cfrpg/Flatcaster/doc/PadArraySim.asc

C1: cap; {Cap0}
C2: cap; {Cap0}
C3: cap; {Cap0}
C4: cap; {Cap0}
C5: cap; {Cap0}
C6: cap; {Cap0}
C7: cap; {Cap0}
C8: cap; {Cap0}
C9: cap; {Cap0}
C10: cap; {Cap1}
C11: cap; {Cap0}
C12: cap; {Cap0}
C13: cap; {Cap0}
C14: cap; {Cap0}
C15: cap; {Cap0}
C16: cap; {Cap0}
C17: cap; {Cap0}
C18: cap; {Cap0}
C19: cap; {Cap0}
C20: cap; {Cap0}
C21: cap; {Cap0}
C22: cap; {Cap0}
C23: cap; {Cap0}
C24: cap; {Cap0}
C25: cap; {Cap0}
C26: cap; {Cap0}
C27: cap; {Cap1}
C28: cap; {Cap0}
C29: cap; {Cap0}
C30: cap; {Cap0}
C31: cap; {Cap0}
C32: cap; {Cap0}
C33: cap; {Cap0}
C34: cap; {Cap0}
C35: cap; {Cap0}
C36: cap; {Cap0}
C37: cap; {Cap0}
C38: cap; {Cap0}
C39: cap; {Cap0}
C40: cap; {Cap0}
C41: cap; {Cap0}
C42: cap; {Cap0}
C43: cap; {Cap0}
C44: cap; {Cap0}
C45: cap; {Cap0}
C46: cap; {Cap0}
C47: cap; {Cap0}
C48: cap; {Cap0}
D1: schottky; BAT54
D3: schottky; BAT54
D4: schottky; BAT54
D5: schottky; BAT54
D6: schottky; BAT54
D7: schottky; BAT54
D8: schottky; BAT54
D9: schottky; BAT54
D10: schottky; BAT54
D11: schottky; BAT54
D12: schottky; BAT54
D13: schottky; BAT54
D14: schottky; BAT54
D15: schottky; BAT54
D16: schottky; BAT54
D17: schottky; BAT54
D18: schottky; BAT54
D19: schottky; BAT54
D20: schottky; BAT54
D21: schottky; BAT54
D23: schottky; BAT54
D24: schottky; BAT54
D25: schottky; BAT54
D26: schottky; BAT54
D27: schottky; BAT54
D29: schottky; BAT54
D30: schottky; BAT54
D31: schottky; BAT54
D32: schottky; BAT54
D33: schottky; BAT54
D35: schottky; BAT54
D36: schottky; BAT54
D37: schottky; BAT54
D38: schottky; BAT54
D39: schottky; BAT54
D41: schottky; BAT54
D42: schottky; BAT54
D43: schottky; BAT54
D44: schottky; BAT54
D45: schottky; BAT54
D47: schottky; BAT54
D48: schottky; BAT54
D49: schottky; BAT54
D50: schottky; BAT54
D51: schottky; BAT54
D53: schottky; BAT54
D54: schottky; BAT54
R1: res; {Res}
R2: res; {Res}
R3: res; {Res}
R4: res; {Res}
R5: res; {Res}
R6: res; {Res}
R7: res; {Res}
R8: res; {Res}
R9: res; {Res}
R10: res; {Res}
R11: res; {Res}
R12: res; {Res}
R13: res; {Res}
R14: res; {Res}
R15: res; {Res}
R16: res; {Res}
R17: res; {Res}
R18: res; {Res}
R19: res; {Res}
R20: res; {Res}
R21: res; {Res}
R22: res; {Res}
R23: res; {Res}
R24: res; {Res}
R25: res; {Res}
R26: res; {Res}
R27: res; {Res}
R28: res; {Res}
R29: res; {Res}
R30: res; {Res}
R31: res; {Res}
R32: res; {Res}
R33: res; {Res}
R34: res; {Res}
R35: res; {Res}
R36: res; {Res}
R37: res; {Res}
R38: res; {Res}
R39: res; {Res}
R40: res; {Res}
R41: res; {Res}
R42: res; {Res}
R43: res; {Res}
R44: res; {Res}
R45: res; {Res}
R46: res; {Res}
R47: res; {Res}
R48: res; {Res}
S1: sw; SWDC
S4: sw; SWDC
S5: sw; SWDC
S6: sw; SWDC
S7: sw; SWDC
S8: sw; SWDC
S9: sw; SWDC
S10: sw; SWDC
V1: voltage; PULSE(0 3.3 10u 0 0 {Tc} {(Tc+Tr)*6})
V2: voltage; PULSE(0 3.3 {10u+(Tc+Tr)} 0 0 {Tc} {(Tc+Tr)*6})
V3: voltage; PULSE(1 0 10u 0 0 {Tc} {Tc+Tr})
V4: voltage; PULSE(0 3.3 {10u+(Tc+Tr)*2} 0 0 {Tc} {(Tc+Tr)*6})
V5: voltage; PULSE(0 3.3 {10u+(Tc+Tr)*3} 0 0 {Tc} {(Tc+Tr)*6})
V6: voltage; PULSE(0 3.3 {10u+(Tc+Tr)*4} 0 0 {Tc} {(Tc+Tr)*6})
V7: voltage; PULSE(0 3.3 {10u+(Tc+Tr)*5} 0 0 {Tc} {(Tc+Tr)*6})
Named nets: 0, T0, T1, T2, T3, T4, T5, T6, T7, IN0, IN1, IN2, IN3, IN4, IN5
.param Cap0=3p Res=470k Cap1=100p Tc=200u Tr=20u
.tran {(Tc+Tr)*20}
.model SWDC sw(Ron=0.1 Roff=1G Vt=0.5)
