cfrpg/Flatcaster/src/v0.1/project/src/at32f435_437_wk_config.c

/* add user code begin Header */
/**
  **************************************************************************
  * @file     at32f435_437_wk_config.c
  * @brief    work bench config program
  **************************************************************************
  *                       Copyright notice & Disclaimer
  *
  * The software Board Support Package (BSP) that is made available to
  * download from Artery official website is the copyrighted work of Artery.
  * Artery authorizes customers to use, copy, and distribute the BSP
  * software and its related documentation for the purpose of design and
  * development in conjunction with Artery microcontrollers. Use of the
  * software is governed by this copyright notice and the following disclaimer.
  *
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
  **************************************************************************
  */
/* add user code end Header */

#include "at32f435_437_wk_config.h"

/* private includes ----------------------------------------------------------*/
/* add user code begin private includes */

/* add user code end private includes */

/* private typedef -----------------------------------------------------------*/
/* add user code begin private typedef */

/* add user code end private typedef */

/* private define ------------------------------------------------------------*/
/* add user code begin private define */

/* add user code end private define */

/* private macro -------------------------------------------------------------*/
/* add user code begin private macro */

/* add user code end private macro */

/* private variables ---------------------------------------------------------*/
/* add user code begin private variables */

/* add user code end private variables */

/* private function prototypes --------------------------------------------*/
/* add user code begin function prototypes */

/* add user code end function prototypes */

/* private user code ---------------------------------------------------------*/
/* add user code begin 0 */

/* add user code end 0 */


/**
  * @brief  config periph clock
  * @param  none
  * @retval none
  */
void wk_periph_clock_config(void)
{
  /* enable gpioa periph clock */
  crm_periph_clock_enable(CRM_GPIOA_PERIPH_CLOCK, TRUE);

  /* enable gpiob periph clock */
  crm_periph_clock_enable(CRM_GPIOB_PERIPH_CLOCK, TRUE);

  /* enable gpioc periph clock */


  /* enable gpioh periph clock */
  crm_periph_clock_enable(CRM_GPIOH_PERIPH_CLOCK, TRUE);

  /* enable dma1 periph clock */
  crm_periph_clock_enable(CRM_DMA1_PERIPH_CLOCK, TRUE);

  /* enable qspi1 periph clock */
  crm_periph_clock_enable(CRM_QSPI1_PERIPH_CLOCK, TRUE);

  /* enable tmr4 periph clock */
  crm_periph_clock_enable(CRM_TMR4_PERIPH_CLOCK, TRUE);

  /* enable spi2 periph clock */


  /* enable spi3 periph clock */
  crm_periph_clock_enable(CRM_SPI3_PERIPH_CLOCK, TRUE);

  /* enable dac periph clock */
  crm_periph_clock_enable(CRM_DAC_PERIPH_CLOCK, TRUE);


  /* enable tmr1 periph clock */
  crm_periph_clock_enable(CRM_TMR1_PERIPH_CLOCK, TRUE);

  /* enable adc3 periph clock */
  crm_periph_clock_enable(CRM_ADC3_PERIPH_CLOCK, TRUE);

  /* enable spi1 periph clock */
  crm_periph_clock_enable(CRM_SPI1_PERIPH_CLOCK, TRUE);
}

/**
  * @brief  nvic config
  * @param  none
  * @retval none
  */
void wk_nvic_config(void)
{
  nvic_priority_group_config(NVIC_PRIORITY_GROUP_2);

  NVIC_SetPriority(MemoryManagement_IRQn, NVIC_EncodePriority(NVIC_GetPriorityGrouping(), 0, 0));
  NVIC_SetPriority(BusFault_IRQn, NVIC_EncodePriority(NVIC_GetPriorityGrouping(), 0, 0));
  NVIC_SetPriority(UsageFault_IRQn, NVIC_EncodePriority(NVIC_GetPriorityGrouping(), 0, 0));
  NVIC_SetPriority(SVCall_IRQn, NVIC_EncodePriority(NVIC_GetPriorityGrouping(), 0, 0));
  NVIC_SetPriority(DebugMonitor_IRQn, NVIC_EncodePriority(NVIC_GetPriorityGrouping(), 0, 0));
  NVIC_SetPriority(PendSV_IRQn, NVIC_EncodePriority(NVIC_GetPriorityGrouping(), 0, 0));
  NVIC_SetPriority(SysTick_IRQn, NVIC_EncodePriority(NVIC_GetPriorityGrouping(), 0, 0));

  nvic_irq_enable(DMA1_Channel1_IRQn, 1, 0);
}

/* add user code begin 1 */

/* add user code end 1 */
