cfrpg/Flatcaster/src/v0.1/project/src/at32f435_437_int.c

#include "at32f435_437_int.h"


/**
  * @brief  this function handles nmi exception.
  * @param  none
  * @retval none
  */
void NMI_Handler(void)
{

}

/**
  * @brief  this function handles hard fault exception.
  * @param  none
  * @retval none
  */
void HardFault_Handler(void)
{
 
  while (1)
  {

  }
}

/**
  * @brief  this function handles memory manage exception.
  * @param  none
  * @retval none
  */
void MemManage_Handler(void)
{

  while (1)
  {

  }
}

/**
  * @brief  this function handles bus fault exception.
  * @param  none
  * @retval none
  */
void BusFault_Handler(void)
{

  while (1)
  {

  }
}

/**
  * @brief  this function handles usage fault exception.
  * @param  none
  * @retval none
  */
void UsageFault_Handler(void)
{

  while (1)
  {
    
  }
}

/**
  * @brief  this function handles svcall exception.
  * @param  none
  * @retval none
  */
void SVC_Handler(void)
{

}

/**
  * @brief  this function handles debug monitor exception.
  * @param  none
  * @retval none
  */
void DebugMon_Handler(void)
{

}

/**
  * @brief  this function handles pendsv_handler exception.
  * @param  none
  * @retval none
  */
void PendSV_Handler(void)
{

}
