cfrpg/Flatcaster/src/v0.1/project/src/drivers/flash.h

#ifndef __FLASH_H
#define __FLASH_H

#include "sys.h"


void flash_read(uint32_t read_addr, uint16_t *p_buffer, uint16_t num_read);
error_status flash_write_nocheck(uint32_t write_addr, uint16_t *p_buffer, uint16_t num_write);
error_status flash_write(uint32_t write_addr,uint16_t *p_Buffer, uint16_t num_write);

#endif
